waywardgeek/infnoise/images/infnoise_brd.png

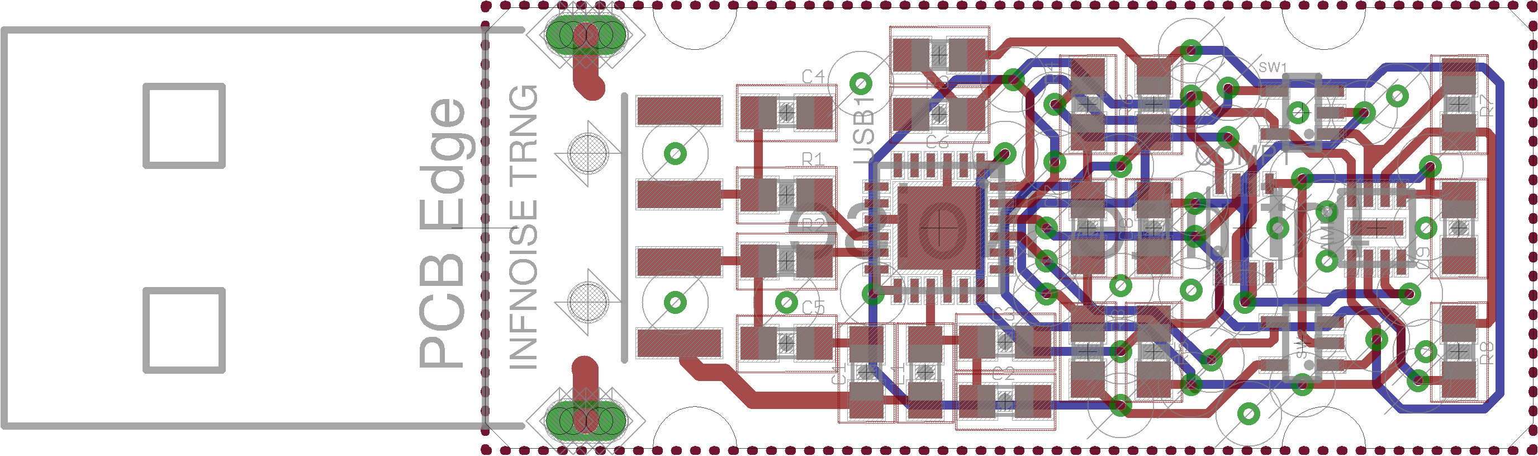
images/infnoise_brd.png
