waywardgeek/infnoise/images/infnoise_breadboard.jpg

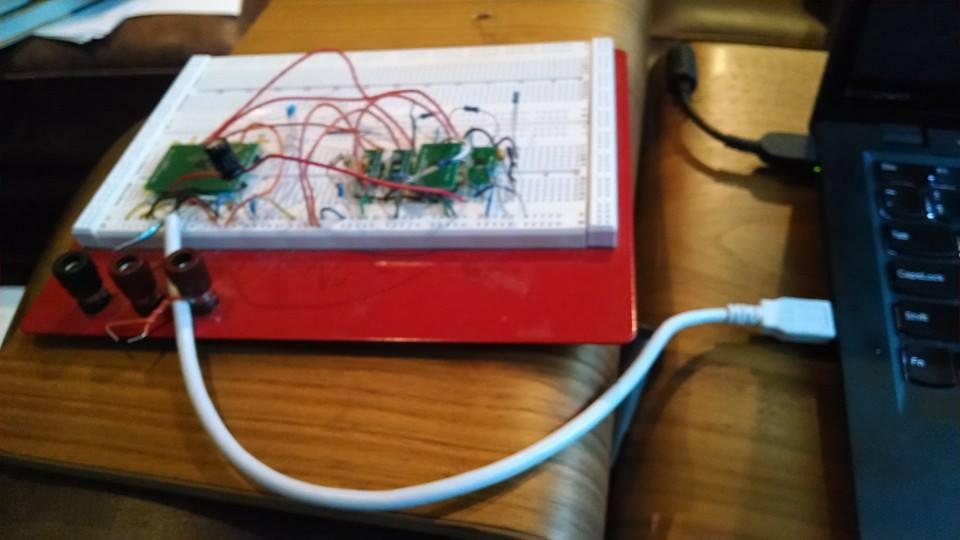
images/infnoise_breadboard.jpg
