waywardgeek/infnoise/images/infnoise_pocket.jpg

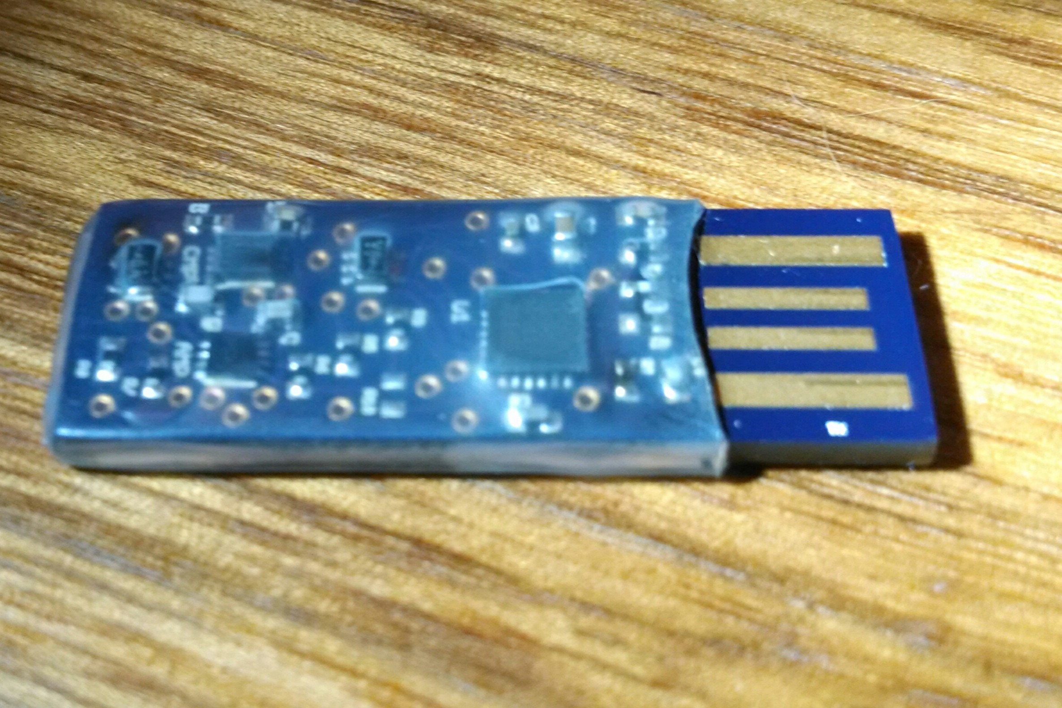
images/infnoise_pocket.jpg
