waywardgeek/infnoise/infnoise_cmos/RNG5.png

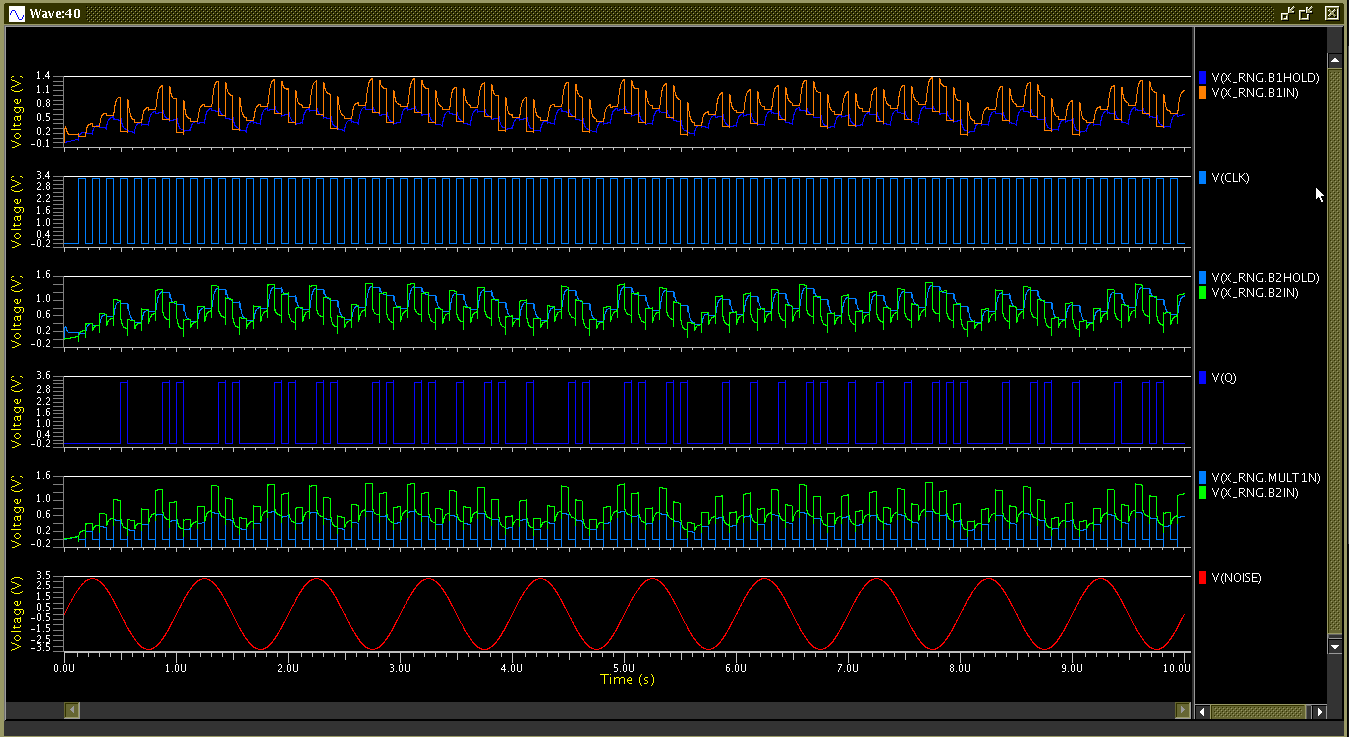
infnoise_cmos/RNG5.png
