waywardgeek/infnoise/infnoise_cmos/schem1.png

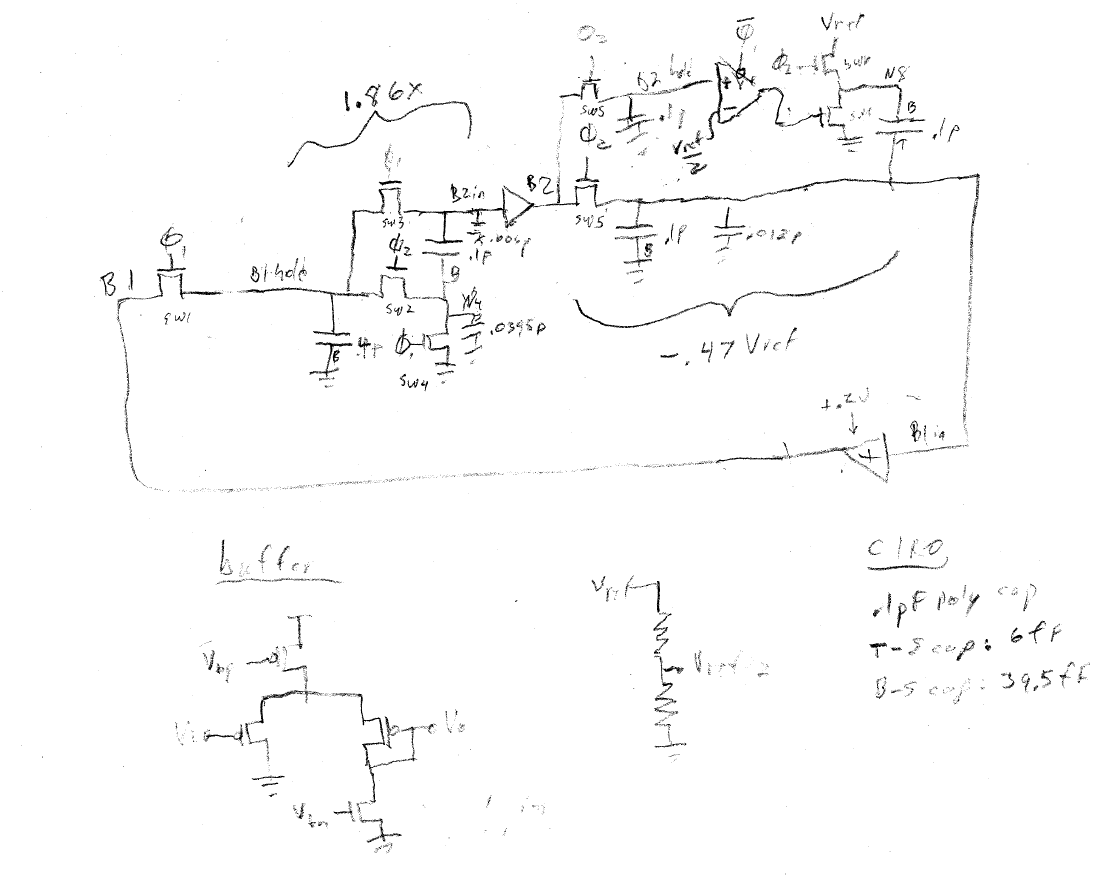
infnoise_cmos/schem1.png
