waywardgeek/infnoise/infnoise_cmos/schem2.png

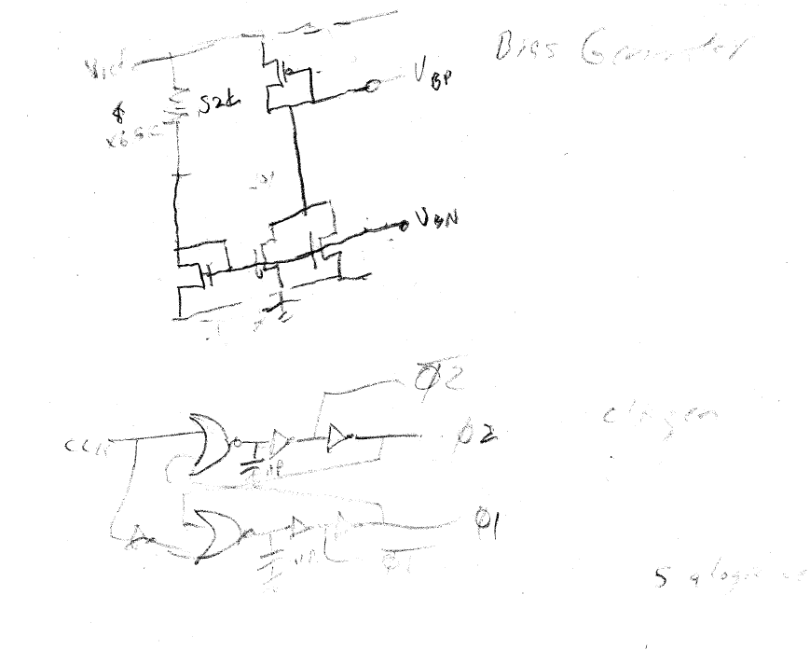
infnoise_cmos/schem2.png
