waywardgeek/infnoise/infnoise_cmos/schem3.png

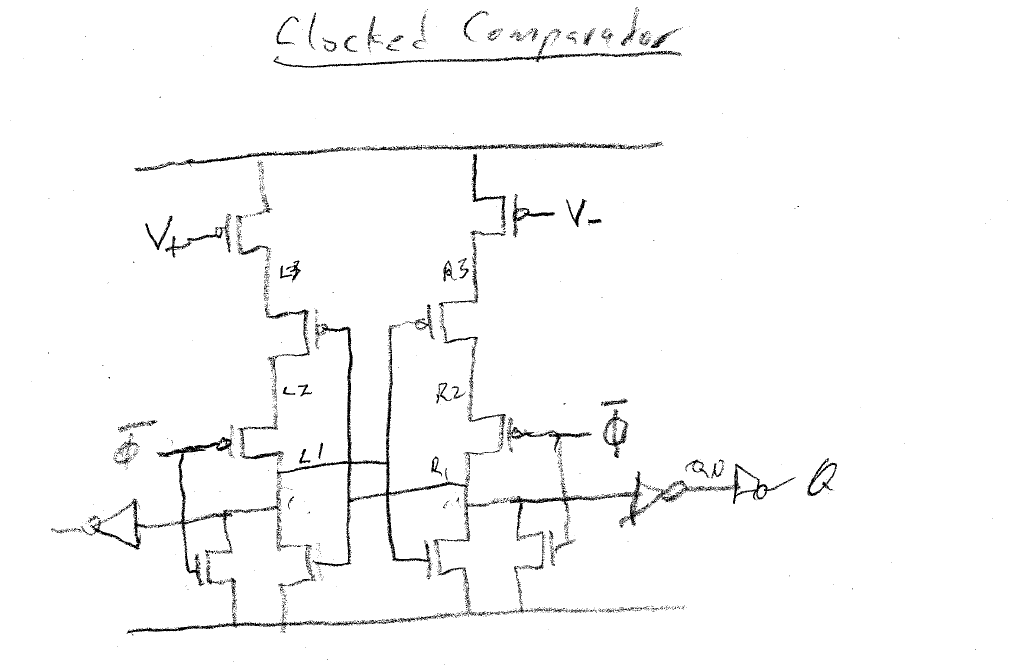
infnoise_cmos/schem3.png
