waywardgeek/infnoise/infnoise_fast/longsim.png

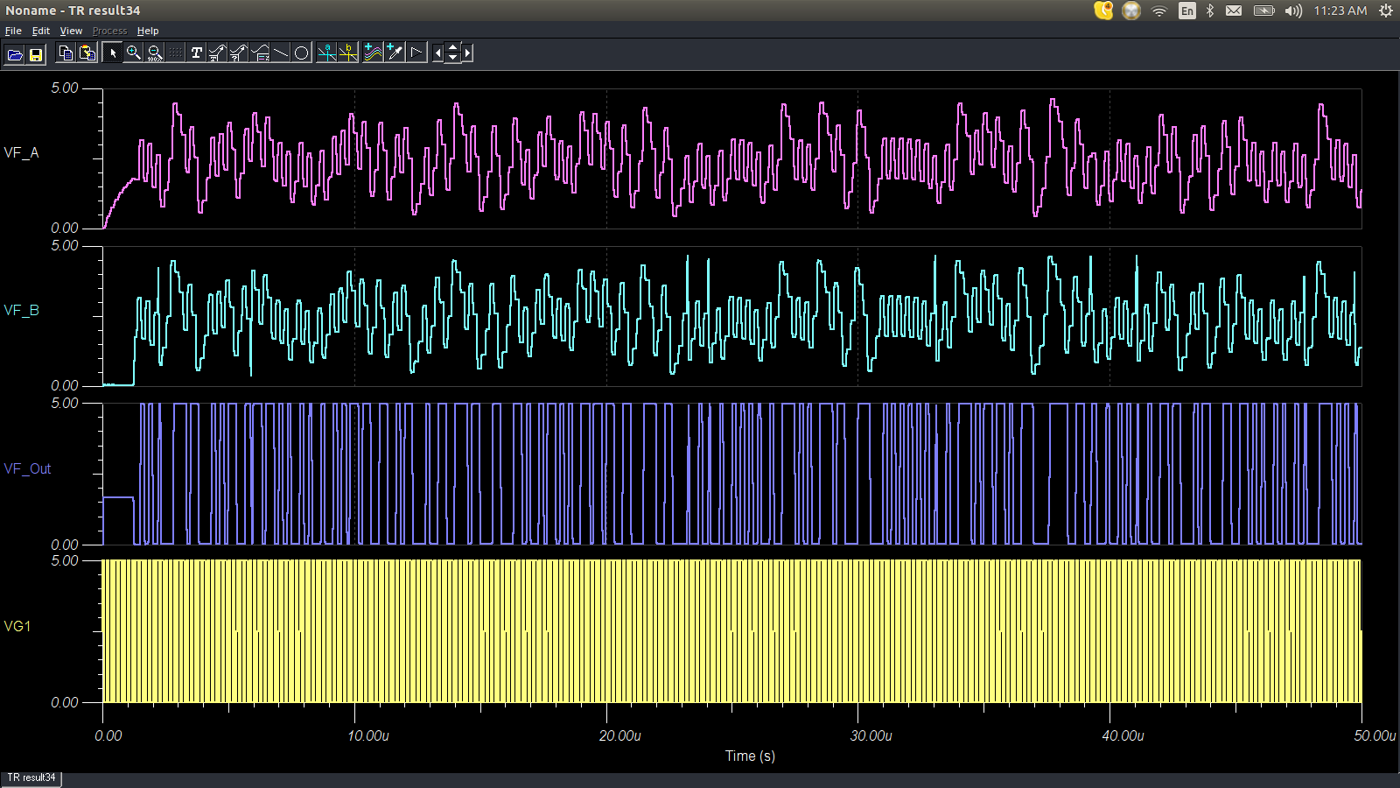
infnoise_fast/longsim.png
