waywardgeek/infnoise/infnoise_fast/shortsim.png

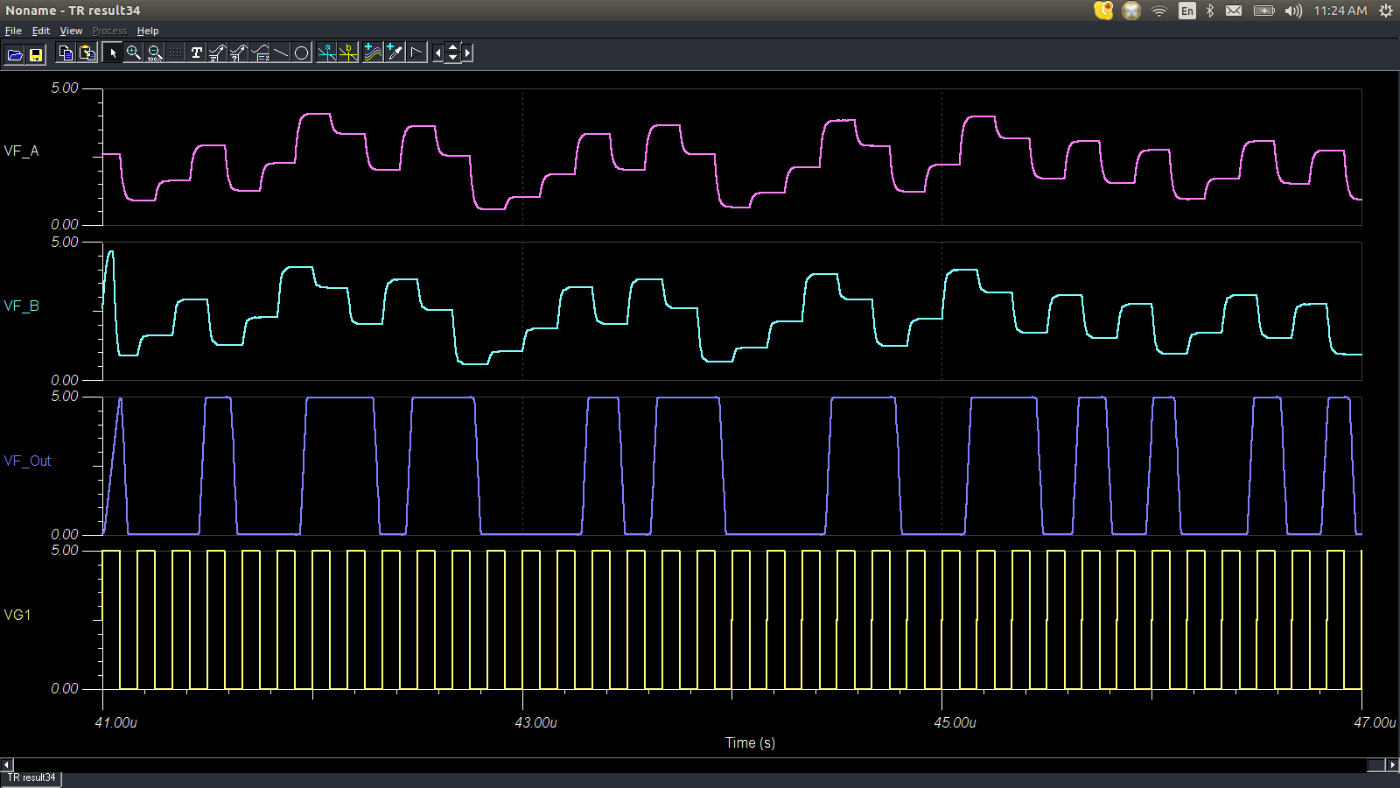
infnoise_fast/shortsim.png
