waywardgeek/infnoise/infnoise_small/longsim.png

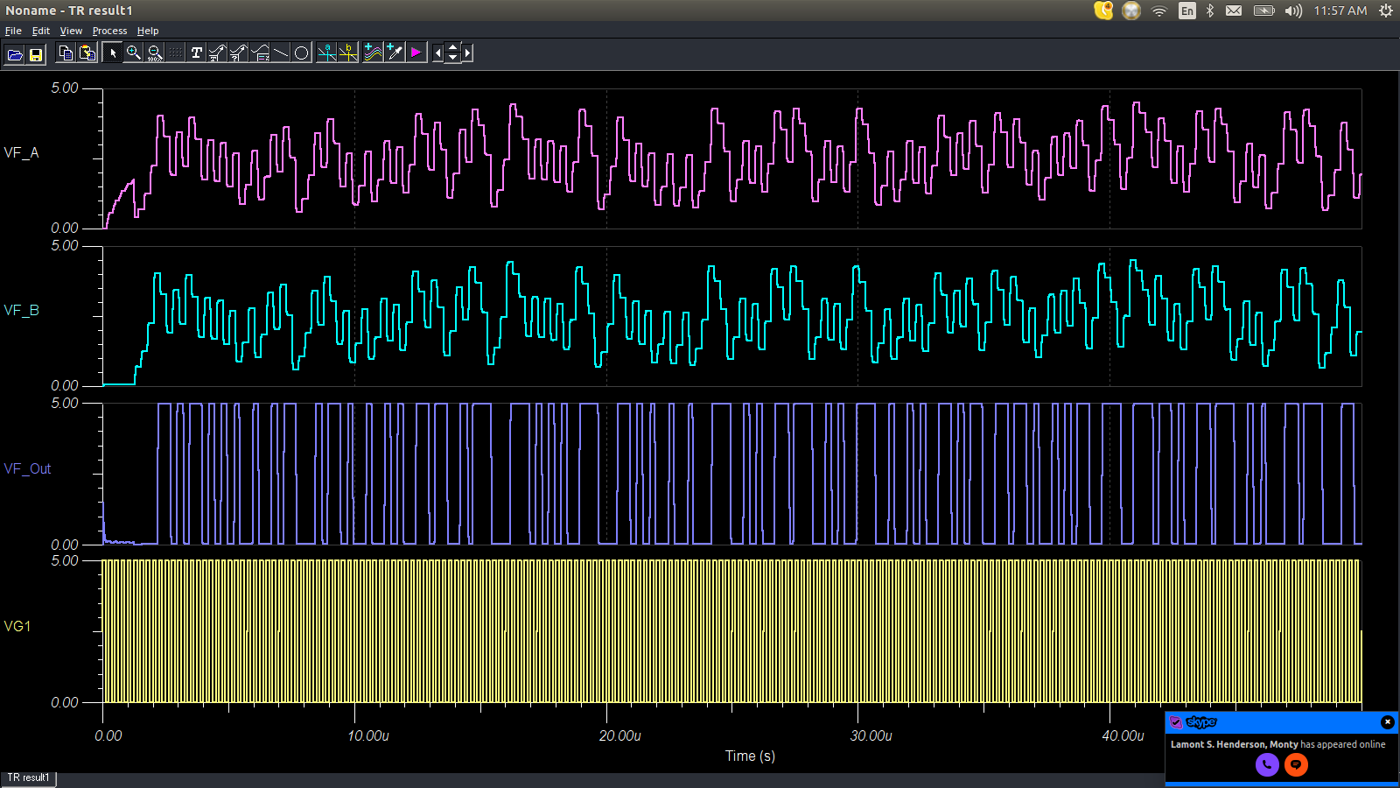
infnoise_small/longsim.png
