waywardgeek/infnoise/infnoise_small/shortsim.png

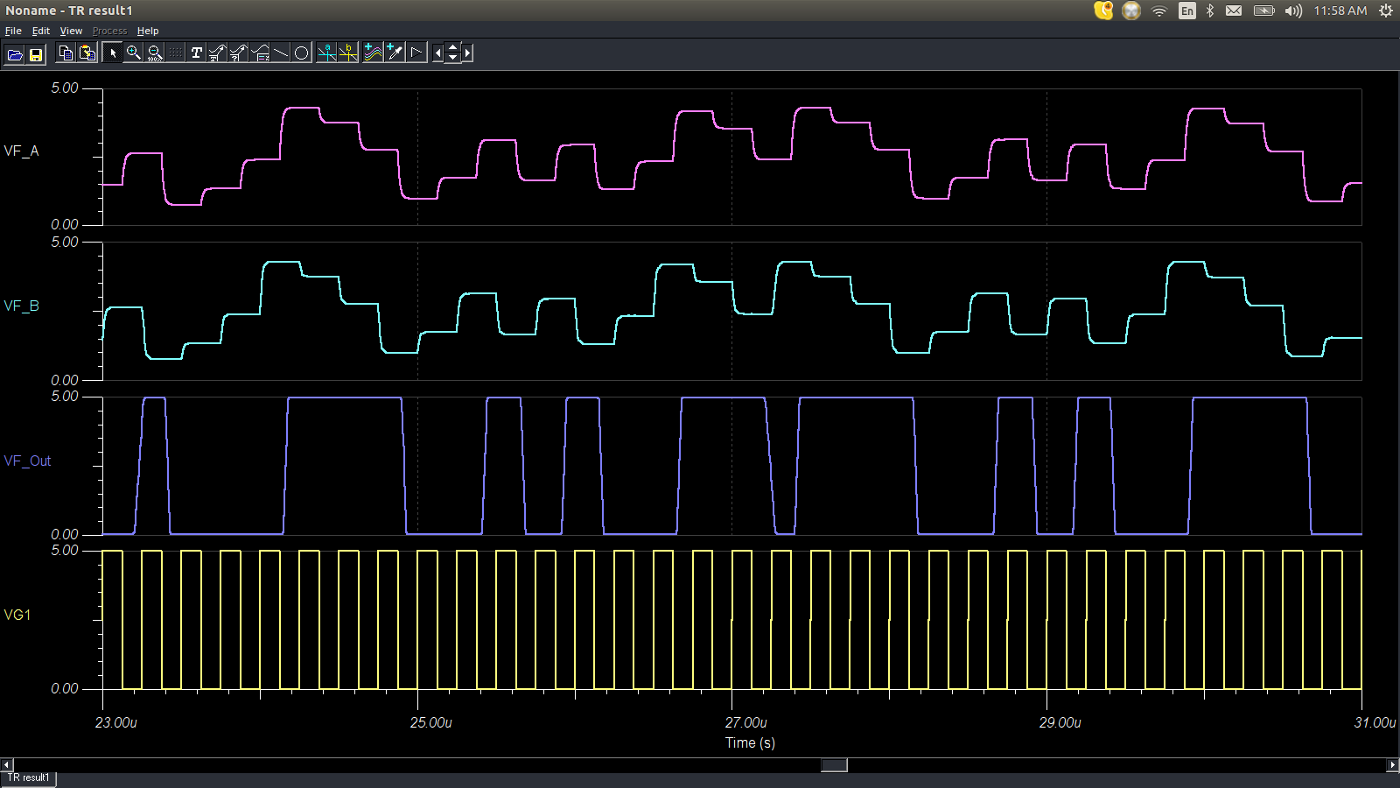
infnoise_small/shortsim.png
