waywardgeek/infnoise/tests/plots/infnoise-raw.bin-scatter.png

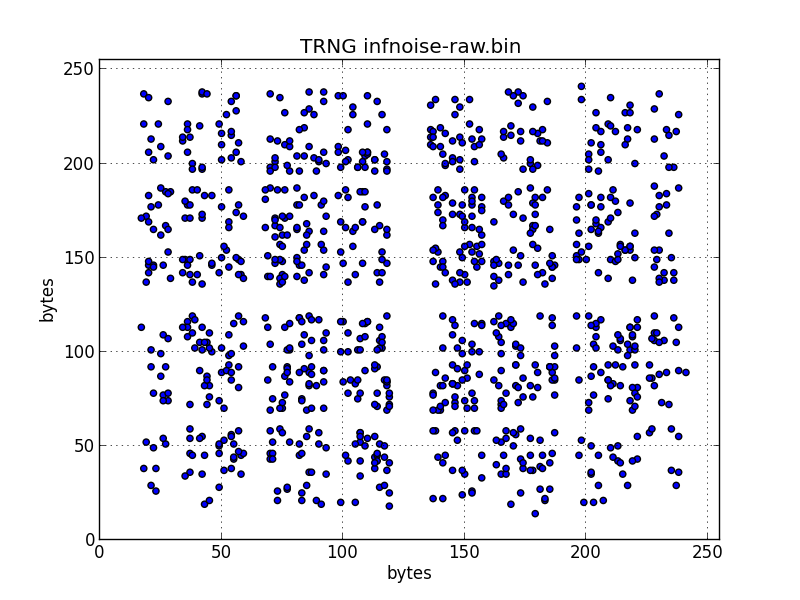
tests/plots/infnoise-raw.bin-scatter.png
