waywardgeek/infnoise/tests/results/v0.3.0/plots/devrandom-1-25000K.out-colormap.png

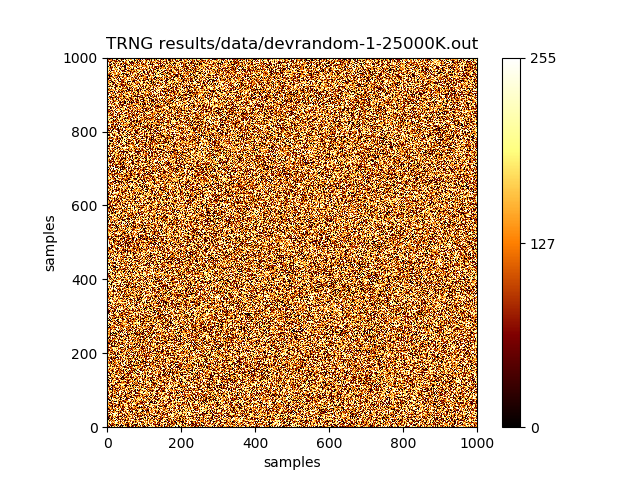
tests/results/v0.3.0/plots/devrandom-1-25000K.out-colormap.png
