waywardgeek/infnoise/tests/results/v0.3.0/plots/devrandom-1000-25000K.out-colormap.png

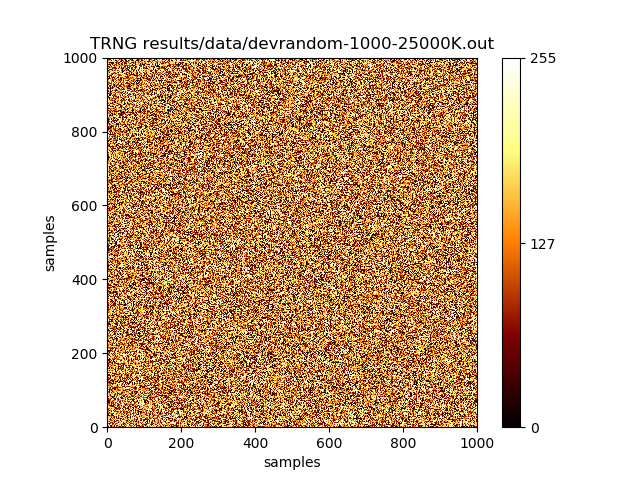
tests/results/v0.3.0/plots/devrandom-1000-25000K.out-colormap.png
