waywardgeek/infnoise/tests/results/v0.3.0/plots/devrandom-10000-25000K.out-scatter.png

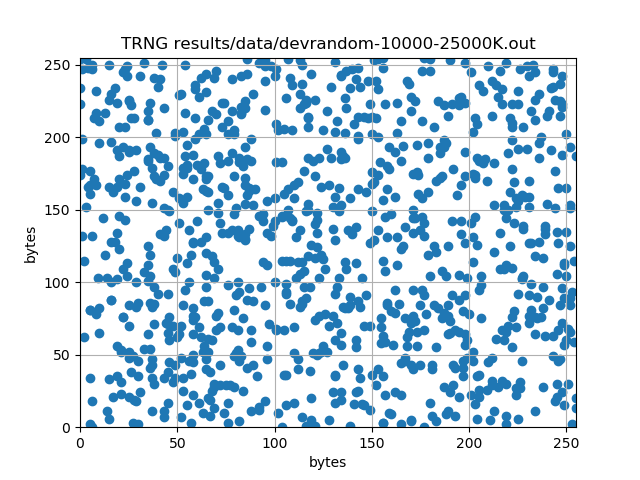
tests/results/v0.3.0/plots/devrandom-10000-25000K.out-scatter.png
