waywardgeek/infnoise/tests/results/v0.3.0/plots/whitened-0-25000K.out-colormap.png

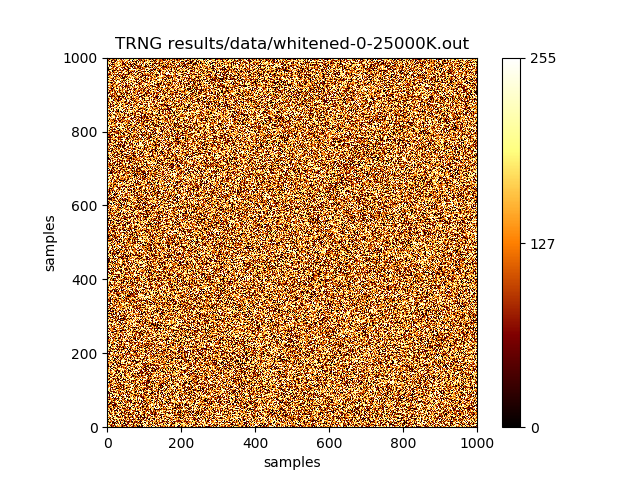
tests/results/v0.3.0/plots/whitened-0-25000K.out-colormap.png
