waywardgeek/infnoise/tests/results/v0.3.0/plots/whitened-1000-25000K.out-scatter.png

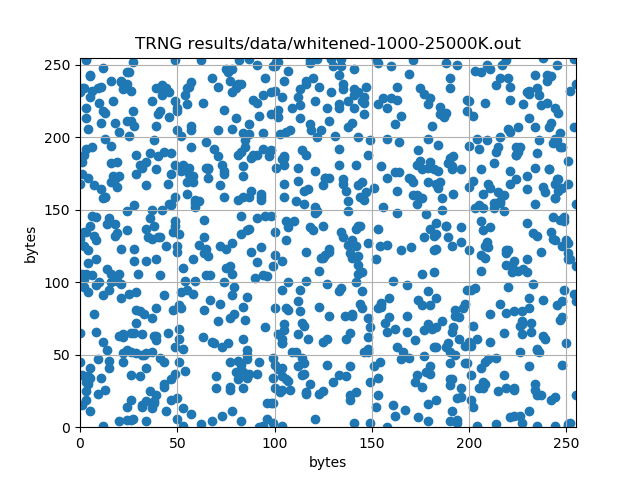
tests/results/v0.3.0/plots/whitened-1000-25000K.out-scatter.png
