waywardgeek/infnoise/software/healthcheck.h

bool inmHealthCheckStart(uint8_t N, double K, bool debug);
void inmHealthCheckStop(void);
bool inmHealthCheckAddBit(bool bit, bool even);
bool inmHealthCheckOkToUseData(void);
double inmHealthCheckEstimateK(void);
double inmHealthCheckEstimateEntropyPerBit(void);
// Returns number of bytes of entropy added so far
uint32_t inmHealthCheckGetEntropyLevel(void);
void inmHealthCheckReduceEntropyLevel(uint32_t numBytes);
